cristianoag/msx-picoverse-public/docs/msx-picoverse-2040-features.md

# MSX PicoVerse 2040 Features

The MSX PicoVerse 2040 is a Raspberry Pi Pico-based MSX-compatible cartridge that offers a variety of features to enhance the MSX experience. Below is a list of its key features:

- **Multi-ROM Support**: The cartridge can store and run multiple MSX ROMs, allowing users to run different games and applications from a single cartridge.
- **Built-in Menu System**: A user-friendly menu system allows users to select and launch ROMs easily.
- **High Compatibility**: Supports a wide range of MSX ROMs, including games and applications for MSX1, MSX2, and MSX2+ systems.
- **Nextor DOS Support**: Compatible with Nextor DOS, enabling advanced file management and storage options.
- **Long Name Support**: Supports ROM names up to 50 characters, making it easier to identify games and applications.
- **Support for Various Mappers**: Includes support for multiple ROM mappers, enhancing compatibility with different types of MSX software. Mappers supported include: PL-16, PL-32, KonSCC, Linear, ASC-08, ASC-16, Konami, NEO-8, NEO-16, and others.
- **Support for up to 128 ROMs**: Can store and manage up to 128 different ROMs on a single cartridge.
- **Easy ROM Management**: Users can easily add, remove, and organize ROMs using a simple tool on their PC.
- **Fast Loading Times**: Utilizes the high-speed capabilities of the Raspberry Pi Pico to ensure quick loading times for games and applications.
- **Firmware Updates**: The cartridge firmware can be updated via USB, allowing users to benefit from new features and improvements over time.
- **Compact Design**: The cartridge is designed to fit seamlessly into MSX systems without adding bulk.
- **USB Mass Storage Support for Nextor**: Allows the use of the USB-C port as a mass storage device when running Nextor DOS.
- **RAM Mapper Support**: Enables the use of additional RAM for applications that require it when running Nextor DOS.
