cristianoag/msx-picoverse-public/2350/software/loadrom.pio/docs/log.md

# Change Log

## PicoVerse 2350 Loadrom v2.79

- Bumped LoadROM version to v2.79 (top-level `Makefile` and `tool/Makefile`).
- Added the `-s3` / `--sunrise3-sd` tool option for testing Nextor 3, microSD only for now. It builds a `Nextor Sunrise 3.0.0 Beta 2 (SD)` system image with Konamiman's Nextor 3.0.0 beta 2 Sunrise IDE MasterOnly kernel (`resources/Nextor-3.0.0-beta2.SunriseIDE.MasterOnly.ROM`, 128 KB, SunriseIDE-Nextor-driver `v0.1.8-blueMSX-v0.1.5-Nextor-3.0-beta.2` release), embedded by `tool/Makefile` as `tool/src/nextor3.h`. It uses the existing Sunrise SD type (15), so the firmware is unchanged; the beta 2 driver sends the same ATA commands as 2.1.4.
- `-s3` is mutually exclusive with the other Nextor modes, rejects a ROM file, `-d` and `-f` like `-s1`, and accepts `-w` (same loader as `-s1`). The tool refuses to build a Nextor image whose kernel is not 128 KB. Checked `-s3`, `-s3 -w` and `-s1` UF2s: the record points at the matching kernel bytes, and with `-w` the ESP8266P BIOS follows it. Booting beta 2 on hardware is not yet validated.
- Docs: LoadROM tool manual (`-s3`, `-w`, exclusivity, example, troubleshooting), Sunrise Nextor implementation notes (option table, MultiROM `-a`/`-s3`, and the stale `nextor/kernel/` paths now point at `resources/`), MegaRAM notes (same path fix), public README and WiFi notes.
- The shared generator `../tools/gen_romdb.py` now downloads the latest database by default from Vampier's ROM DB (`https://romdb.vampier.net/Archive/xml-msxromsdb.zip`) and reads `softwaredb.xml` from the zip in memory, so a local openMSX install is no longer needed. A local `softwaredb.xml` or `.zip` can still be passed as an argument for offline use. The generated header now records the source and the database timestamp. The script also accepts the `ASCII16-X` and lowercase `konami` mapper names used by this database.
- Regenerated `tool/src/romdb.h` from the 2026-10-03 database: 3115 → 3218 entries (103 added, none removed or changed), including 31 ASCII16-X ROMs (mapper 12) that the old DB never matched. Rebuilt `tool/dist/loadrom.exe`.

## PicoVerse 2350 Loadrom v2.78

- Simplified the standalone OPL4 (`-4`) generation options by removing `--opl4-limit` (adaptive PCM voice limiter) and `--lowclock` (282 MHz system clock). The tool now rejects both as unknown options, and `--22khz` is the remaining OPL4 option for extreme-polyphony songs.
- The OPL4 firmware always runs the RP2350 at 300 MHz (`OPL4_SYS_CLOCK_KHZ`) and always renders all 24 PCM voices: the voice-cap controller and its Core 1 hook were removed from `opl4_main.c`, and `ymf278b::generate` in `ymfm_opl.cpp` is back to the upstream `pcm_engine::ALL_CHANNELS` output mask. The per-buffer fill-time measurement is now only compiled in USB debug builds, and the debug report drops its `cap=` and `limit=` fields.
- The 16-byte `PVO4` config header between the firmware and the YRW801-M ROM is kept so the flash layout is unchanged; its flags byte is now reserved and always written as 0, and the firmware only uses the header to locate the ROM.
- Archived the removed code, grouped by the source file it came from, in `2350/software/old/loadrom_opl4_voice_limiter.c` and `2350/software/old/loadrom_opl4_lowclock.c`.
- Updated the LoadROM tool manual, the OPL4 implementation guide and the public readme to drop both options and point dense-song playback to `--22khz`.
- Bumped the loadrom build version to v2.78 (top-level and tool Makefiles), and regenerated the embedded 44.1 kHz and 22.05 kHz OPL4 firmware payloads.

## PicoVerse 2350 Loadrom v2.77

- Fixed the `.FLA` image being written to the microSD card empty, which left ASCII16-X FlashROM saves working only when a valid image happened to be there already. Creating the image was deferred until the MSX actually programmed the flash, and the file has to be opened with `FA_CREATE_ALWAYS`, which truncates it to zero straight away; the rest was then written only after the MSX had been quiet for a while. A game that saves and is then switched off left a zero-byte or partial file on the card, and because the restore path requires the file to match the emulated device size exactly, the next boot rejected it and started over. The image is now created in full during cartridge start-up, before the bus goes live, so the file on the card is always a complete, valid image.
- Bumped the loadrom build version to v2.77 (top-level and tool Makefiles).

## PicoVerse 2350 Loadrom v2.76

- Implemented the FlashROM half of the [ASCII16-X specification](https://www.grauw.nl/projects/ascii-x/ascii16-x/), so ASCII16-X cartridges can now erase and reprogram their own memory the way the real hardware does. Games and tools that use it for save games, high scores or user created levels work instead of silently failing.
- FlashROM emulation is opt-in through the `ASC16X-FR` filename tag, the same tag the Explorer tool uses, so a ROM tagged for one tool behaves the same way in the other. Auto-detection is unchanged: a ROM recognised as ASCII16-X is always built as the read-only variant, which keeps the previous behaviour and ignores flash command sequences entirely, so nothing changes for the ASCII16-X ROMs that never write to the cartridge. The two paths are separate bus loops, so the read-only one carries no extra work per bus cycle.
- Replaced the `-fr`/`--flashrom` option this feature originally shipped with; the tag is now the only way to select it, matching how every other mapper is forced in this tool. `ASC-16X-FR` is accepted as an alias, and `ASC16X` was added as an alias for the read-only variant so Explorer's spelling of both tags works here too.
- FlashROM stays a flag bit on mapper 12 rather than becoming a mapper number of its own as it is in Explorer (22). LoadROM packs the audio flags into the upper nibble of the mapper byte, so the firmware decodes a non-SYSTEM mapper as `rom_type & 0x0F` and only values 1-15 are addressable - mapper 22 would decode to 6 (ASCII16) and silently run the wrong mapper. The tag is what the user sees in both tools; only the on-flash encoding differs.
- The emulated device follows the AMD/Spansion command set the specification names as the guaranteed minimum: autoselect (`90h`), CFI query (`98h`), chip erase (`10h`), sector erase (`30h`), byte program (`A0h`) and the `F0h` software reset. Command addresses are decoded on A0-A11 (`XAAAh`/`X555h`), which is what the flash chip sees through the mapper, so a command cycle that lands on a bank register mirror updates both, exactly as on the cartridge.
- Sector geometry matches the layout the specification documents: eight 8KB boot sectors followed by 64KB sectors. Erasing clears the whole sector even when it spans several mapper banks.
- Erases run in 256-byte chunks between bus cycles instead of in one blocking pass, and while one is in progress every read returns a busy status byte (DQ7 low, DQ6 toggling, DQ3 set) rather than array data. That is the behaviour the specification tells software to poll for, and it keeps the MSX serviced throughout instead of stretching `/WAIT` for the length of the erase. Flash commands issued while an erase is running are ignored, as they are on the real device, so a stray program cannot corrupt the sector being erased and a second erase cannot abandon the first.
- The CFI records are built for the emulated device size at boot, so a driver that queries the chip gets a consistent description of the geometry it is being given. Only the commands that are actually implemented are advertised: no write buffer, no erase suspend and no sector protection, so CFI-driven software cannot pick a programming algorithm the cartridge does not support.
- Fixed flash chip detection failing outright (reported with "Go Figure v1.2", which reported no flash chip). The S29GL064S the ASCII-X cartridges use is a 16-bit device wired in byte mode, so the chip decodes command cycles on *word* addresses and places its identifiers and CFI records at word offsets, which the MSX sees at every second byte address. The emulation had been written as if the chip were an 8-bit part, so it looked for the unlock and query cycles at the wrong addresses and returned the identity bytes from the wrong offsets. Command decoding now ignores the lowest address bit, the CFI query is recognised at `X0AAh` instead of `X055h`, and the autoselect identifiers and CFI records are returned as 16-bit values split across even and odd byte addresses. Checked against the actual cycles the game issues: it queries CFI with `98h` to `40AAh` and reads `4020h`/`4022h`/`4024h` for `QRY`, then unlocks with `AAh` to `4AAAh` and `55h` to `4554h` before `90h` selects autoselect and it reads the manufacturer at `4000h` and the device identifiers at `4002h`, `401Ch` and `401Eh`. Note that the sector erase and byte program sequences were unaffected, because the address the game uses for their second unlock cycle happened to satisfy the old check as well.
- Reworked where the flash array lives. With the tag applied, the cartridge ROM is staged into the external PSRAM at boot and that copy is the writable flash array, with the existing 256KB SRAM bank cache in front of it so MSX reads are still served from internal SRAM at full speed. The previous flash handling only modified the SRAM cache, so any write was lost as soon as its bank was evicted, and a bank refill re-read the unmodified ROM from flash.
- With the tag applied, the emulated device is sized to the next power of two at or above the ROM size (minimum 64KB, capped at the 8MB PSRAM), so banks past the end of the ROM read as erased (`FFh`) and out-of-range bank numbers wrap at the device size, matching a real cartridge. The read-only path keeps wrapping at the ROM size as before.
- Added `storage/flash_sd.c`, which mirrors the flash array to a `.FLA` file in the root of the microSD card named after the cartridge, so flash writes survive a power cycle. The file has no header: it is a byte exact image of the cartridge flash and can be copied off the card and used as a ROM image.
- At boot Core 1 mounts the card and restores the image when a file of the expected size is present. The MSX is held in `/WAIT` for that read, and the bus is only released once Core 1 has finished with the array so the bank cache can never be filled from a half-restored image. When no usable image is present nothing is written at boot: creating one means writing the whole array to the card, which takes seconds on a multi-megabyte cartridge, so it is deferred until the MSX actually programs the flash and then runs on Core 1 with the bus already live. A card that has never been saved to therefore costs nothing at startup. Afterwards Core 1 writes back only the 4KB blocks the MSX modified, and only once the MSX has left the flash alone for 250 ms, so a burst of byte programs turns into a handful of card writes. A failed restore falls back to the embedded ROM rather than leaving a half-replaced image behind, and a block whose write or sync fails is put back on the queue instead of being dropped.
- Flash emulation degrades gracefully: without working PSRAM the mapper still runs from the ROM in firmware flash, and without a usable microSD the flash is emulated normally but is volatile. Persistence is also skipped when `-d` (second PSG) is used with an ASCII16-X ROM, because that emulation already owns the core that writes the card.
- The PC tool now reports whether FlashROM emulation is on for ASCII16-X ROMs, and when it is, the emulated device size and the name of the `.FLA` image it will use. It warns when `-d` disables persistence, lists `ASC16X-FR` among the forceable tags in `-h`, and tells the user which tag to apply when a ROM was detected as plain ASCII16-X.
- Bumped the loadrom build version to v2.76 (top-level and tool Makefiles).

## PicoVerse 2350 Loadrom v2.75

- Fixed OPL4/MoonSound images (`-4`, with or without `--22khz`) playing much quieter than the SCC, PSG and MSX-MUSIC audio profiles, which forced the amplifier or TV volume to be turned far up for an OPL4 game and back down again afterwards (reported with "Go Figure"). The YMF278B emulation core applies no output normalisation to this chip - upstream marks its YMF278B mixing as unverified - so the cartridge was running about 7 dB below the level the same hardware plays SCC/PSG music at. The final output stage now applies a 3x gain, which lines the OPL4 up with the other profiles.
- The gain was calibrated against openMSX, whose wave part is matched to real MoonSound recordings, by comparing the peak one voice or channel can contribute to an output channel: openMSX puts a MoonSound wave voice at 0.292 of full scale, an SCC channel at 0.102 and a PSG channel at 0.255, while the PicoVerse firmware puts its SCC channel at 0.200 and its PSG channel at 0.498 - a consistent ~1.96x above openMSX - against only 0.85x for the OPL4 wave voice. The FM/wave balance is unchanged: both halves of the emulated chip already peak at the same per-channel level openMSX gives them, so the correction is a single gain on the mixed output and the chip's own mix registers (0xF8/0xF9) still set the balance.
- Replaced the hard clip on the OPL4 output with the same soft-knee limiter the SCC and MSX-MUSIC profiles use. The chip can key 24 wave voices and 18 FM channels at once, so a sum over full scale is normal on dense songs; the mix is now compressed smoothly toward full scale instead of being squared off into harsh buzz, and a single maximum-level voice still passes through untouched.
- Added `OPL4_OUTPUT_GAIN_NUM`/`OPL4_OUTPUT_GAIN_SHIFT` CMake options (default 96/32 = 3x) so the output level can be A/B tested from the build configuration alone.
- The OPL4 USB debug report now prints `lim/s` (samples pushed past the limiter knee) in place of `clip/s`, which measured a hard clip that no longer exists.
- Bumped the loadrom build version to v2.75 (top-level and tool Makefiles), and regenerated the embedded 44.1 kHz and 22.05 kHz OPL4 firmware payloads.

## PicoVerse 2350 Loadrom v2.74

- Added the `--22khz` option to the standalone OPL4 mode (`-4`). It builds an OPL4 cartridge image that renders audio at 22050 Hz instead of 44100 Hz, roughly halving the emulation workload. This is meant for the handful of very dense songs (reported with "Go Figure") that use so many simultaneous FM channels and wave voices that the 44.1 kHz emulation cannot keep up in real time and breaks into continuous noise. The trade-off is a duller high end and more aliasing on bright FM patches, cymbals and high-pitched samples, so the option is opt-in and the default 44.1 kHz image remains the recommended one.
- The 22 kHz image still emulates every FM channel and wave voice at full polyphony: instead of dropping voices, each generated sample simply covers twice as much chip time, with the wave positions, FM phase, envelopes and LFOs advanced accordingly so pitch, tempo and envelope timing are unchanged.
- The OPL4 USB debug report now includes the output sample rate, so a capture states which of the two images produced it.
- Fixed occasional video glitches seen when a game running from a second cartridge shares the MSX with a `--22khz` OPL4 cartridge. The wave part reports a "loading" status bit for about 300 us after every instrument change, and music drivers poll that bit before continuing. The delay was counted in generated samples rather than in real time, so at 22050 Hz it lasted twice as long, doubling the time the MSX spent in that polling loop - long enough to push a raster-timed game routine past its deadline. The count is now scaled with the output rate, so the host sees the same 300 us in both images.
- Fixed notes sounding too quiet, or not being heard at all, on some songs with `--22khz`. The fastest wave envelope rates step on every emulated sample period, so at the reduced output rate they were advancing at half speed. Short percussive notes never reached full volume before the next event, and the fast "damp" used to silence a voice before reassigning it took twice as long. Both the wave and FM envelope generators now replay the sample periods a reduced-rate build steps over, and were verified against the 44100 Hz build to better than half a percent across the whole attack and release.
- Fixed missing FM notes, most noticeable on songs using many FM channels (reported with "Neon Horizon"). A note retrigger writes key-off then key-on for the same channel, and the FM part only looked at the key signal once per generated sample, so a retrigger that arrived inside one sample collapsed into "still on" and the note never restarted. This is the same defect that was fixed for the wave part in v2.72, and it applied to the FM part as well; it shows up far more often with `--22khz` because that sample window is twice as long and the cartridge applies a whole burst of MSX writes between two samples. Key changes are now applied in the order the MSX issues them. Debug captures ruled out the alternatives: the emulation was comfortably real-time throughout, with no late buffers, no dropped writes and no clipping.
- Fixed OPL4 debug builds not being detected by software that probes for the cartridge at boot. The debug firmware waits up to five seconds for a USB host to attach, and that wait ran before the cartridge brought up its MSX bus responder, so the OPL4 was absent from the bus for the whole timeout and a game checking for it at startup (reported with "Neon Horizon") ran without music. The wait now happens after the bus is live. Production builds were never affected.
- Bumped the loadrom build version to v2.74 (top-level and tool Makefiles).

## PicoVerse 2350 Loadrom v2.73

- Fixed hanging notes in OPL4 playback, most noticeable at music transitions (reported with Bombaman). The wave part has a "pseudo-reverb" feature that lets a note ring out at a fixed slow rate once it drops below -18 dB. That state was also being entered *after* the MSX had already released the note, and it overrode both the instrument's own release rate and the damp command the music driver uses to silence a voice, so released notes kept sounding for many seconds instead of stopping. Pseudo-reverb is now only entered while a note is still held, and an explicit key-off always takes a released voice back to its programmed release rate. Debug telemetry confirmed the cause: during every hang the firmware reported that all the ringing voices had already been released by the MSX.
- Fixed occasional dropped OPL4 register writes during normal playback. The audio core holds the emulation lock for the whole of each generated sample - about two thirds of the time available - so the bus core could sit blocked long enough for the 8-entry hardware write FIFO to fill and silently lose MSX writes. The bus core now keeps emptying that FIFO into its much larger software queue while it waits for the lock, and also between register writes, which can each take a while when a new instrument has to be fetched from memory. Debug captures had shown the overflow flag being raised in 8 of 118 seconds of Bombaman playback.
- Added the voices sitting in the pseudo-reverb envelope (`pcmRev`) to the OPL4 USB debug report, so a hanging-note report can be checked against the envelope state that causes it.
- Bumped the loadrom build version to v2.73 (top-level and tool Makefiles).

## PicoVerse 2350 Loadrom v2.72

- Fixed missing instruments in OPL4 MOD playback (reported with MOP playing `enigma.mod`). A note retrigger writes key-off then key-on for the same voice, and when both arrived within the same emulated sample the pair was merged into a single "still on" state, so the note never restarted and that voice fell silent. Key changes are now applied in the order the MSX issues them.
- Fixed audible clicks, crackle and noise on dense OPL4 songs (reported with Bombaman and Pumpkin Adventure 3). The emulation was spending most of its per-sample time budget on voices that were silent, leaving it right at - and sometimes over - the real-time limit, which starved the audio output. Silent voices are now skipped, cutting the load to roughly a quarter of the budget.
- Fixed hanging and delayed notes caused by the cartridge freezing the MSX for about 150 us on every OPL4 register read. During read bursts this stole up to a quarter of the CPU time from the running music replayer. The read handler now answers about fifteen times faster, which also makes OPL4 sample uploads roughly three times quicker.
- Fixed the optional adaptive voice limiter (`--opl4-limit`) leaving hanging notes: dropped voices froze mid-note instead of being silenced, and resumed where they left off when the limiter recovered.
- Improved the OPL4 USB debug report with true output-clipping detection, the number of voices actually being rendered, and the voices the MSX asked to play, so audio complaints can be traced to the right stage. Removed some per-sample debug work that was distorting the timing figures it reported.
- Extended the OPL4 USB debug report with the key-offs the MSX issued and the voices still sounding after being released (`pcmOff`, `pcmRel`), which separates a lost key-off from a release envelope that simply takes a long time to fade - both are heard as a hanging note.
- Added build options to individually disable this version's OPL4 changes (`OPL4_SKIP_INACTIVE_FM`, `OPL4_SKIP_INACTIVE_PCM`, `OPL4_READ_SYNC_IDLE_SPINS`) so a regression can be narrowed down from the build configuration alone. Defaults keep all the fixes enabled.
- Bumped the loadrom build version to v2.72 (top-level and tool Makefiles).

## PicoVerse 2350 Loadrom v2.71

- Bumped the loadrom build version to v2.71 (top-level and tool Makefiles).
- Fixed the standalone OPL4 firmware asserting `/BUSDIR` on bus cycles that do not belong to it. The dedicated `/BUSDIR` state machine inferred "an OPL4 read is in progress" purely from `/WAIT` being low, but `/WAIT` is a shared open-drain MSX bus signal, so any second cartridge stretching its own cycles made the OPL4 flip the main-board data-bus buffer towards the CPU. `msx_opl4_busdir` now tests `/IORQ` (new `jmp_pin`, matching the MSX-AUDIO firmware) before asserting, so memory cycles driven by another cartridge are ignored.
- Changed the standalone OPL4 write captor (`msx_opl4_io_write`) to commit register/memory writes on the `/WR` rising edge. The GPIO snapshot is still taken well inside `/WR` low, where the Z80 write data is valid, but the RX FIFO push (which triggers the PIO IRQ and the `opl4_bus_write()` call) was happening before `wait 1 gpio 25`, so the emulated YMF278B could apply a write while the CPU had not finished the bus cycle. The push now happens after the `/WR` rise, matching how a real chip latches.
- Applied the same `/WR` rising-edge commit to the standalone MSX-AUDIO firmware: both `msxaudio_io_write` (Y8950 ports 0xC0/0xC1) and `msxaudio_mem_write` (ADPCM sample RAM window) now sample the bus inside `/WR` low but only push to the RX FIFO once `/WR` has risen.

## PicoVerse 2350 Loadrom v2.70

- Bumped the loadrom build version to v2.70 (top-level and tool Makefiles).
- Fixed lost bank-switch writes in the ASCII16, ASCII16-X, Neo-8 and Neo-16 mapper loops. Those loops blocked in `pio_get_read_servicing_dual_psg()` and only drained the memory write captor FIFO *after* a cartridge read arrived, so game code executing from MSX RAM that issued a burst of segment switches without any intervening cartridge read overflowed the 8-entry RX FIFO. The write state machine then stalled on `push block` and the extra switches were silently dropped, leaving the mapper register on a stale segment (and, with an ASCII16-X cache miss, forcing the 16KB bank refill to run while `/WAIT` was already asserted). Added `pio_get_read_draining_writes()`, which services the dual-PSG I/O and drains the memory write FIFO while waiting for the next read, and switched the four loops to it. Reported with "Go Figure v1.2" (ASCII16-X), which alternates the page-1 segment twice per call from a page-3 RAM routine and hung on the palette cross-fade. The Konami/Konami-SCC/ASCII8 `banked8_loop` already drained writes while idle and was unaffected.
- Kept the idle loop at the same read-response latency as a plain blocking wait by sampling `FSTAT` once per iteration and testing the read and write RX-empty flags from that single sample. Polling the two FIFOs with separate `pio_sm_is_rx_fifo_empty()` calls doubles the PIO register accesses in the loop, which stretches `/WAIT` on every cartridge read enough to slow VDP transfer loops and trigger "VDP too slow" reports in timing-sensitive games (observed on the RP2040 build). `banked8_loop` now shares the same helper instead of its own inline poll, so Konami/Konami-SCC/ASCII8 reads got the same latency reduction.

## PicoVerse 2350 Loadrom v2.69

- Bumped the loadrom build version to v2.69 (top-level and tool Makefiles) and added the `msxaudio` build target, with `tool` depending on it.
- Reorganized `pico/loadrom` sources into per-type subfolders: `audio/` (`emu2149`, `emu2212`, `emu2413`), `memory/` (`c2_emu`, the Carnivore2-style mapper/RAM emulation), and `storage/` (`hw_config`, `sunrise_ide`, `sunrise_sd`), updating `CMakeLists.txt` and `loadrom.c` includes accordingly. Verified with a full reconfigure and rebuild.
- Removed the unused `wifi_uart.pio` PIO program (superseded by the hardware UART1 ESP-01 backend) and updated the `CMakeLists.txt` comment accordingly.
- Moved `nextor/kernel/Nextor-2.1.4.SunriseIDE.MasterOnly.ROM` into `resources/`, updated the `NEXTOR_SUNRISE` path in `tool/Makefile`, and fixed the resulting `xxd`-generated embed symbol names in `tool/src/loadrom.c`.
- Added a new standalone MSX-AUDIO (Yamaha Y8950) cartridge firmware, selectable with the new `-a` / `--msx-audio` tool option. The cartridge emulates a Y8950 on I/O ports 0xC0/0xC1 with 256KB of ADPCM sample RAM and exposes the MSX-Audio BIOS in its own slot, so MSX-AUDIO software runs on real hardware without an original card. The option is standalone and cannot be combined with any other mode or a ROM file. Issue #25.
- Used the BSD-licensed ymfm `y8950` core for the emulation, kept as a private copy under the new firmware so it does not share sources with the standalone OPL4 firmware. Fixed an upstream ymfm defect that made ADPCM sample RAM read-backs always return 0.
- Added Y8950 FM timer interrupts through the MSX `/INT` line so timer-paced MSX-AUDIO replayers run at the correct tempo, and drove `/BUSDIR` during MSX-AUDIO port reads to avoid bus contention when a second cartridge is installed.
- Added the MSX-AUDIO-only `--4mhz` option, which clocks the emulated Y8950 at 4 MHz instead of the standard 3.579545 MHz. Partially related to issue #33.
- Fixed MSX-AUDIO instruments sounding harsher and different from openMSX on some games (reported with "Wolf of the Battlefield - Commando"). The emulated Y8950 output already leaves the sound core as a full-scale, DAC-clipped 16-bit sample, so the extra 1.5x volume boost that the other PicoVerse audio profiles use was clipping it a second time on loud passages and adding distortion harmonics. The MSX-AUDIO output now runs at unity gain.
- Added `docs/msx-picoverse-2350-msx-audio.md` with the full MSX-AUDIO implementation documentation.
- Documented the standalone MSX-AUDIO (`-a`, `--4mhz`) and OPL4 / MoonSound (`-4`, `--opl4-limit`, `--lowclock`) builds in `docs/msx-picoverse-2350-features.md`, `docs/msx-picoverse-2350-loadrom-tool-manual.en-us.md`, and `docs/msx-picoverse-public-readme.md`, including slot/port maps, sample RAM, `/INT` timer behavior, output rates, standalone mutual-exclusion rules, troubleshooting rows, and MSX-AUDIO credits. Also corrected the manual's stale OPL4 `--22khz` option, which no longer exists in the tool.
- Known limitations: the Philips NMS-1205 MIDI interface and the Music Module's 8-bit DAC on port 0x0A are not emulated.

## PicoVerse 2350 Loadrom v2.68

- Removed the OPL4-only `--22khz` build option and its alternate 22050 Hz standalone firmware payload after validation showed missing instruments and notes in OPL4 playback. The tool now always packages the default 44100 Hz standalone OPL4 firmware for `-4` / `--opl4` images.
- Simplified the standalone OPL4 build and embedding pipeline back to a single firmware artifact (`opl4.bin`) so the main build no longer configures, compiles, embeds, or cleans a separate 22.05 kHz variant.
- Version bumped to v2.68 (top-level and tool Makefiles).

## PicoVerse 2350 Loadrom v2.67

- Added the OPL4-only `--22khz` tool option for `-4`/`--opl4` images. The build now produces and embeds a second dedicated OPL4 firmware payload compiled for 22050 Hz; that variant advances FM/PCM/timer state by two normal OPL4 sample periods per generated output sample so pitch and tempo stay at normal speed while reducing output-rate workload. Default OPL4 UF2s continue to use the 44100 Hz firmware.
- Version bumped to v2.67 (top-level and tool Makefiles).

## PicoVerse 2350 Loadrom v2.66

- Fixed the PC tool mapper-detection read path to reject truncated ROM reads before hashing or scanning the allocated ROM buffer.
- Version bumped to v2.66 (top-level and tool Makefiles).

## PicoVerse 2350 Loadrom v2.65

- Bumped the loadrom build version to v2.65.
- Gated the standalone OPL4 USB diagnostic counters out of production builds so timer/IRQ debug increments and output peak globals are only compiled when `OPL4_USB_DEBUG` is enabled.

## PicoVerse 2350 Loadrom v2.64

- Bumped the loadrom build version to v2.64.
- Added `-r1`/`--megaram-sd` and `-r2`/`--megaram-usb` Nextor system images with the existing Sunrise IDE ROM, a 1MB MSX memory mapper, and a new 1MB PSRAM-backed MegaRAM subslot.

## PicoVerse 2350 Loadrom v2.63

- Tuned the standalone OPL4 adaptive PCM voice limiter to be less aggressive: it now lowers the voice cap only after sustained late buffers, restores voices after repeated headroom, and keeps a higher minimum cap so melodic leads are less likely to be ducked when `--opl4-limit` is enabled.

## PicoVerse 2350 Loadrom v2.62

- Bumped the loadrom build version to v2.62.
- Expanded the standalone OPL4 `OPL4DBG` USB CDC report with timer, read latency, write FIFO/ring-drop, limiter, and clock-mode counters for field captures of missing-instrument issues, while keeping USB CDC disabled by default for normal timing validation. Left enabled by default so we can capture data in case of future reports of missing instruments or other audio issues.
- Added the OPL4-only `--lowclock` tool option for `-4`/`--opl4` images; default OPL4 UF2s keep the 300 MHz RP2350 clock, while `--lowclock` marks the OPL4 config header so the firmware boots at 282 MHz. This is to cover low quality PSRAM modules that cannot sustain the 300 MHz clock at full polyphony, which can cause audio underruns and missing instruments. The firmware reads the config header and sets the RP2350 clock divider to 282 MHz if the option is present.
- Raised the standalone OPL4 firmware's final I2S output gain to better match the SCC, MSX-MUSIC, and other emulated audio profiles while preserving signed 16-bit clipping protection (issue reported by Peter).
- Regenerated the embedded standalone OPL4 firmware payload and rebuilt the loadrom tool so the `loadrom -4` image uses the intended 300 MHz RP2350 clock instead of a stale 250 MHz binary (issue reported by Peter).

## PicoVerse 2350 Loadrom v2.61

- Updated the public README OPL4 credits to describe the PicoVerse 2350 standalone MoonSound firmware architecture, host-port handling, YMF278B/ymfm wrapper, YRW801-M ROM/RAM model, and third-party reference/ROM attribution more accurately.
- Fixed Neo-8/Neo-16 ROMs not launching when MSX-MUSIC/FM-PAC (`-f` / `-fmpac`) is enabled (the same ROM booted fine without `-f`). The FM-PAC expanded-slot launcher reset the Neo-8/Neo-16 bank windows to `{0,1,2,...}`, exposing segment 1 at MSX `0x4000`, so the cartridge "AB" boot header (which lives in segment 0) was hidden during the BIOS expanded-slot scan and the MSX dropped to BASIC. The windows now power on at segment 0 (`{0,0,0,...}`), matching the standalone `loadrom_neo8`/`loadrom_neo16` loaders, so the header is visible at `0x4000` and the game launches alongside FM-PAC.
- Fixed MSX-MUSIC/FM-PAC ROMs (`-f` / `-fmpac`) booting to BASIC instead of launching the game. The firmware was starting the YM2413 Core 1 + I2S audio output in `main()` *before* `loadrom_fmpac()` ran the expanded-slot cold-boot bootstrap, so the running audio core/DMA perturbed the timing-critical FM-PAC bus handshake and the MSX dropped to BIOS. The audio output launch (`msx_music_start_audio()`) is now deferred until after the bootstrap completes and `msx_pio_bus_init()` has brought the FM-PAC bus responder live — matching the Explorer ordering ("start MSX-MUSIC audio output only after the FM-PAC ROM bus initialization releases `/WAIT`"). `main()` now only runs `msx_music_init()` (emulator setup) for the MSX-MUSIC audio mode.
- Refreshed the generated ROM mapper SHA1 database from the current openMSX `softwaredb.xml` and updated the shared generator to parse the new attribute-based XML format.
- Changed the standalone OPL4 cartridge `/BUSDIR` driver from open-drain to push-pull so it matches a real OPL4/MoonSound cartridge (the WozBlaster CPLD drives `/BUSDIR = /RD & /CS` as a continuous push-pull output). The dedicated PIO2 state machine now drives the line actively HIGH when released and LOW only while answering an OPL4 I/O read, instead of releasing it to hi-Z. The previous open-drain release could let the MSX data-bus-buffer direction input float during register writes on machines without a strong `/BUSDIR` pull-up, occasionally corrupting OPL4 register writes and dropping instruments from some songs; driving it push-pull keeps the buffer direction defined at all times.
- Added an optional adaptive PCM voice limiter to the standalone OPL4 cartridge, selectable at programming time with the new `loadrom -4 --opl4-limit` option. Extreme-polyphony homebrew (e.g. Neon Horizon) drives the full YMF278B ~1.6-1.9x past the single-core real-time synthesis budget, underrunning the I2S and producing harsh broken audio. When the limiter is enabled, Core 1 measures its own per-buffer fill time and dynamically lowers the number of rendered PCM voices (`ymf278b::generate` renders only voices `[0, cap)`) just enough to stay real-time, raising the cap back toward the full 24 when the load eases. Light passages stay bit-identical; only the densest peaks shed their highest-numbered PCM voices, trading some peak polyphony for continuous, in-tune playback instead of underrun noise. The option is off by default (full fidelity, may underrun on extreme songs); the firmware reads the choice from a 16-byte config header the tool writes between the firmware image and the appended YRW801-M ROM.

## PicoVerse 2350 Loadrom v2.60

- Bumped the loadrom version to v2.60.
- Major OPL4/MoonSound overhaul with a new dual-core architecture on the RP2350, significantly improving compatibility, stability, and performance.
- Full MoonSound support now working correctly, including successful operation with MoonTest, SETOPL4, MBWAVE, and MoonBlaster.
- Fixed critical OPL4 emulation issues, improving compatibility with software that relies on accurate YMF278B behavior, status reporting, and memory access.
- Added proper OPL4 timer interrupt support through the MSX /INT line, allowing music players and replayers to run at the correct tempo.
- Corrected FM timer timing, fixing playback speed problems that previously caused some MoonSound applications to run extremely slowly.
- Improved audio synthesis performance, enabling real-time playback at full polyphony through SRAM execution, optimized memory access, and a 300 MHz RP2350 clock speed.
- Redesigned the OPL4 write handling path, eliminating dropped register writes during heavy audio workloads and improving reliability in complex games and music software.
- Updated /WAIT signal handling to use open-drain behavior, preventing conflicts when multiple cartridges are installed in the MSX.
- Held /WAIT asserted during the brief OPL4 boot initialization so the Z80 (and any game in another cartridge slot) is frozen until the cartridge's bus responder is live, fixing cases where a second cartridge's game started — and began its MoonSound music — before the OPL4 cartridge was ready. The hold spans only the sub-millisecond PSRAM/ymfm bring-up (well under the Z80 DRAM-refresh limit) and is released when the PIO takes over /WAIT; the PSRAM-init failure path releases /WAIT so the MSX can still boot.
- Added advanced OPL3 diagnostic capabilities to investigate remaining audio differences in a small number of FM-only titles.
- Compiled the YMF278B synthesis core (the ymfm sources and the `emu278b` wrapper) at `-O3 -funroll-loops` instead of the SDK default `-O2`, since they are the firmware's hottest per-sample path and sit at the real-time budget under maximum polyphony. The change is optimization-only (bit-identical audio) and gives extra instruction-level throughput; it does not fully resolve the documented extreme-polyphony ceiling but recovers a small amount of headroom.
- Drove the MSX `/BUSDIR` line (GPIO 37) during OPL4 I/O read responses, matching how a real OPL4/MoonSound cartridge behaves (the WozBlaster CPLD asserts `/BUSDIR = /RD & /CS`). The cartridge now flips the MSX main-board data-bus buffer toward the CPU only while it answers one of its own ports (0x7E/0x7F, 0xC4-0xC7) and drives D0-D7; otherwise `/BUSDIR` is released hi-Z (open-drain). Previously `/BUSDIR` was left as an unused input, so the firmware's data-bus drive fought the host's slot data buffer on every OPL4 read — visible as screen flashing / graphics artifacts (without a freeze) when a game in another cartridge slot was also driving the bus. Because `/BUSDIR` (GPIO 37) lies outside the 32-pin window the read/write state machines use for A0-A7, it is driven by a dedicated state machine on PIO2 (GPIO base 16) that mirrors the read responder's selection: it holds `/BUSDIR` low from the moment the read SM asserts `/WAIT` for an OPL4 port until `/RD` is released.
- Removed the temporary `OPL4_DRIVE_INT` diagnostic build switch; the `/INT` line is once again always driven from the YMF278B FM-timer interrupt. The switch had been added to test whether the maskable-interrupt path caused the multi-cartridge graphics-corruption crash, but that was ruled out — the cause was the missing `/BUSDIR` drive above.
Production-ready release, with hardware validation completed and accompanying implementation documentation added.

## PicoVerse 2350 Loadrom v2.59

- Bumped the loadrom sub-project version to v2.59.
- Added a dedicated, standalone OPL4 / YMF278B / MoonSound / WozBlaster cartridge firmware under `pico/opl4/`. This firmware implements a MoonSound-compatible OPL4 register interface and exposes the YRW801-M ROM as directly mapped wave memory, allowing it to pass the full MoonTest OPL4 detection and RAM test sequence without any host-side patches or timing compromises. The cartridge is built with the new `-4` / `--opl4` option in the loadrom tool, which produces a firmware-only UF2 with the OPL4 firmware and YRW801-M ROM embedded back-to-back in flash; this option is mutually exclusive with all other modes and external ROM files.
- Tightened the standalone OPL4 read/write synchronization window so `/WAIT`-held reads only proceed after the decoded write FIFO is empty and `/WR` has remained released long enough for rare MoonTest RAM readback edges.
- Added lock-free FM and wave register readback shadows for software such as MBWAVE that probes the cartridge by reading back recently written OPL4 register/data ports.
- Expanded the standalone OPL4 lock-free host facade to mirror the YMF278 PCM register file more completely: reset defaults, masked device/control bits, address-register auto-increment readback, memory-data readback, and queued PCM control/register writes for the audio core while keeping host memory transfers direct and non-busy.
- Reduced sporadic MoonTest RAM-test errors by keeping PCM memory-window control/address writes local to the lock-free host facade while memory access mode is active, using volatile PSRAM byte accesses for host RAM transfers, and sampling decoded MSX write data later inside the `/WR` low window.
- Removed the experimental Core1 synthesis pause because it did not improve MoonTest RAM stability and could interfere with repeated SETOPL4 `/P` ROM sample playback when tools leave the memory-access-mode bit enabled.
- Hardened USB diagnostics so debug builds never enqueue per-byte `0x7F`/wave-register-`0x06` memory read/write events while memory access mode is active, preventing MoonTest RAM loops from flooding the debug ring and perturbing bus timing.
- Changed the standalone OPL4 audio core to drain queued ymfm writes before each small audio chunk instead of once per 256-sample audio buffer, reducing key-on, wavetable, mixer, SETOPL4, and MBWAVE register latency without the per-sample locking overhead that made tracker playback crawl.

## PicoVerse 2350 Loadrom v2.58

- Bumped the loadrom sub-project version to v2.58.
- Raised the MSX-MUSIC/FM-PAC audio output gain to match the existing SCC, SCC+, and Dual PSG I2S volume boost while preserving sample clipping protection.
- Fixed embedded Sunrise+Mapper SD and Carnivore2 SD/USB type decoding so system type values 16-18 are not mistaken for audio-flagged external ROMs.

## PicoVerse 2350 Loadrom v2.57

- Bumped the loadrom sub-project version to v2.57.
- Added dual PSG emulation: a secondary AY-3-8910 instance (emu2149) clocked at 1.7897725 MHz that captures `OUT (0x10),A` / `OUT (0x11),A` on the MSX I/O bus via a dedicated PIO1 write captor and streams its mix to the I2S DAC alongside the existing SCC audio path.
- Added the loadrom tool `-d` / `--dual-psg` flag that sets bit 4 of the configuration `rom_type` byte; the firmware reads this flag at boot to enable the dual PSG engine.
- Centralised cartridge audio configuration in the firmware as a single mutually-exclusive `audio_mode_t` (`NONE` / `SCC` / `SCC_PLUS` / `DUAL_PSG`) so future on-cartridge sound chips can be plugged in without conflicting with existing engines.
- Enforced audio-mode exclusivity in the tool: `-d` is rejected against `-scc`/`-sccplus`, against Konami SCC and Manbow2 mappers (whose second audio slot is reserved for the on-cartridge SCC chip), and against the embedded Sunrise/Carnivore2 system modes that already use core 1 for storage backends.
- Simplified the `-d` rejection message for Konami SCC / Manbow2 ROMs to "Second PSG is not supported with Konami SCC ROMs."
- Moved dual PSG I/O servicing to core 1 (the audio producer core) so secondary PSG port writes are consumed continuously even while game code runs from MSX RAM and no cartridge read cycles occur.
- Delayed the PIO1 I/O write sample point inside `/WR` low so plain `0x10`/`0x11` port writes are latched after the address and data lines have fully settled.
- Added the shared PicoVerse 2350 Dual PSG implementation reference covering LoadROM and Explorer behavior.
- Added MSX-MUSIC/YM2413 emulation for non-SYSTEM ROMs through `-f` / `-fmpac`, capturing OPLL writes on I/O ports `0x7C`/`0x7D` via PIO1 and streaming emu2413 audio through the I2S DAC.
- Enforced MSX-MUSIC as a mutually-exclusive cartridge audio mode with SCC, SCC+, and Dual PSG; documented the emu2413 credit in the public README.
- Embedded the English FM-PAC BIOS (`FMPCCMFC.BIN`) into the LoadROM tool output for every `-f` / `-fmpac` non-SYSTEM ROM image and exposed it from the firmware through an expanded FM-PAC subslot.
- Added firmware handling for FM-PAC memory-mapped YM2413 registers (`0x7FF4`/`0x7FF5`), FM-PAC control/page registers, and PAC SRAM key gating while preserving the selected game mapper in the primary subslot.
- Updated the 2350 LoadROM manual and public copyright notes to describe FM-PAC BIOS inclusion and credit the bundled BIOS/translation sources.
- Added a detailed PicoVerse 2350 MSX-MUSIC / FM-PAC implementation guide covering the tool packaging, UF2 layout, firmware audio path, expanded-slot BIOS exposure, mapper routing, and limitations.
- Updated the public README with user-facing LoadROM instructions for MSX-MUSIC/FM-PAC and Dual PSG command-line builds.
- Removed Konami SCC and Manbow2 from the supported MSX-MUSIC/FM-PAC mapper set; the LoadROM tool now rejects `-f` / `-fmpac` for those ROMs and the firmware FM-PAC wrapper no longer carries SCC-class mapper branches.
