cristianoag/msx-picoverse-public/2350/software/explorer.pio/msx/src/menu_ui.c

// MSX PICOVERSE PROJECT
// (c) 2026 Cristiano Goncalves
// The Retro Hacker
//
// menu_ui.c - MSX Explorer menu screen rendering and text-mode handling
//
// This work is licensed  under a "Creative Commons Attribution-NonCommercial-ShareAlike 4.0 International
// License". https://creativecommons.org/licenses/by-nc-sa/4.0/

#include <string.h>
#include <stdint.h>
#include "menu_ui.h"
#include "menu.h"
#include "menu_input.h"

__at (BIOS_HWVER) unsigned char msx_version;
__at (BIOS_LINL40) unsigned char text_columns;
__at (BIOS_RG4SAV) unsigned char vdp_reg4;

#define MENU_UI_HLINE_SOURCE_CHAR 0x17
#define MENU_UI_HLINE_PRINT_CHAR  0x7E

static unsigned char menu_ui_render_shortcuts(unsigned char content_width);
static unsigned char menu_ui_shortcuts_length(void);

static void clear_rows_vram(unsigned char start_row, unsigned char end_row, unsigned char width) __naked
{
    (void)start_row;
    (void)end_row;
    (void)width;
    __asm
    ld      hl, #2
    add     hl, sp
    ld      e, (hl)
    inc     hl
    ld      d, (hl)
    inc     hl
    ld      c, (hl)

    ld      a, d
    sub     e
    jr      z, clear_rows_done
    ld      b, a

    ld      hl, (#BIOS_TXTNAM)
    ld      a, e
    ld      e, c
    ld      d, #0
    or      a
    jr      z, clear_rows_calc_done

clear_rows_calc_loop:
    add     hl, de
    dec     a
    jr      nz, clear_rows_calc_loop

clear_rows_calc_done:
clear_rows_loop:
    push    bc
    push    de
    push    hl
    ld      a, #32
    ld      b, #0
    ld      iy,(#BIOS_EXPTBL-1)
    push    ix
    ld      ix,#BIOS_FILVRM
    call    BIOS_CALSLT
    pop     ix
    pop     hl
    pop     de
    pop     bc
    add     hl, de
    djnz    clear_rows_loop

clear_rows_done:
    ret
    __endasm;
}

// blit_row_vram - Copy `width` bytes from a RAM buffer straight into the text
// name table at the given row using BIOS LDIRVM, replacing per-character CHPUT. 
static void blit_row_vram(unsigned char row, const char *src, unsigned char width) __naked
{
    (void)row;
    (void)src;
    (void)width;
    __asm
    ld      hl, #2
    add     hl, sp
    ld      b, (hl)        ; B = row
    inc     hl
    ld      e, (hl)        ; src low
    inc     hl
    ld      d, (hl)        ; DE = src
    inc     hl
    ld      c, (hl)        ; C = width

    push    de             ; save src
    push    bc             ; save row(B) + width(C)

    ; dest = TXTNAM + row * width
    ld      l, c           ; HL = width
    ld      h, #0
    ex      de, hl         ; DE = width
    ld      hl, #0
    ld      a, b           ; A = row
    or      a
    jr      z, blit_addr_done

blit_addr_loop:
    add     hl, de
    dec     a
    jr      nz, blit_addr_loop

blit_addr_done:
    ld      de, (#BIOS_TXTNAM)
    add     hl, de         ; HL = dest VRAM address
    ex      de, hl         ; DE = dest VRAM

    pop     bc             ; B = row, C = width
    ld      b, #0          ; BC = width (length)
    pop     hl             ; HL = src

    ld      iy,(#BIOS_EXPTBL-1)
    push    ix
    ld      ix,#BIOS_LDIRVM
    call    BIOS_CALSLT
    pop     ix
    ret
    __endasm;
}

int menu_ui_supports_80_column_mode(void) {
    return msx_version >= 1;
}

const char *menu_ui_status_text(const char *text_40, const char *text_80) {
    return use_80_columns ? text_80 : text_40;
}

static void menu_ui_copy_char_pattern(unsigned char source_char, unsigned char target_char)
{
    unsigned int base = ((unsigned int)vdp_reg4) << 11;
    unsigned int source_address = base + ((unsigned int)source_char * 8);
    unsigned int target_address = base + ((unsigned int)target_char * 8);

    for (unsigned char i = 0; i < 8; i++) {
        Vpoke(target_address + i, Vpeek(source_address + i));
    }
}

void menu_ui_set_text_mode(int enable_80) {
    if (enable_80) {
        text_columns = 80;
        use_80_columns = 1;
        name_col_width = NAME_COL_WIDTH_80;
    } else {
        text_columns = 40;
        use_80_columns = 0;
        name_col_width = NAME_COL_WIDTH;
    }
    __asm
    ld     iy,(#BIOS_EXPTBL-1)
    push   ix
    ld     ix,#BIOS_INITXT
    call   BIOS_CALSLT
    pop    ix
    __endasm;

    menu_ui_copy_char_pattern(MENU_UI_HLINE_SOURCE_CHAR, MENU_UI_HLINE_PRINT_CHAR);
}

void menu_ui_init_text_mode(void) {
    int enable_80 = (!MENU_FORCE_40_COLUMNS && menu_ui_supports_80_column_mode());
    menu_ui_set_text_mode(enable_80);
}

void invert_chars(unsigned char startChar, unsigned char endChar)
{
    unsigned int srcAddress, dstAddress;
    unsigned char patternByte;
    unsigned char i, c;
    unsigned int base = ((unsigned int)vdp_reg4) << 11;

    for (c = startChar; c <= endChar; c++)
    {
        srcAddress  = base + ((unsigned int)c * 8);
        dstAddress = srcAddress + (96 * 8);

        for (i = 0; i < 8; i++)
        {
            patternByte = Vpeek(srcAddress + i);
            patternByte = ~patternByte;
            Vpoke(dstAddress  + i, patternByte);
        }
    }
}

int menu_ui_try_toggle_columns(void) {
    int target_80 = !use_80_columns;
    if (target_80) {
        if (MENU_FORCE_40_COLUMNS) {
            menu_ui_wait_key_with_blinking_status("80-col off");
            menu_ui_clear_last_line();
            return 0;
        }
        if (!menu_ui_supports_80_column_mode()) {
            menu_ui_wait_key_with_blinking_status("No 80-column");
            menu_ui_clear_last_line();
            return 0;
        }
    }
    menu_ui_set_text_mode(target_80);
    invert_chars(32, 126);
    return 1;
}

unsigned char menu_ui_row_width(void) {
    return (unsigned char)(use_80_columns ? 80 : SCREEN_WIDTH);
}

void menu_ui_clear_rows(unsigned char start_row, unsigned char end_row) {
    if (start_row >= end_row) {
        return;
    }
    clear_rows_vram(start_row, end_row, menu_ui_row_width());
}

void menu_ui_print_title_line(void) {
    if (use_80_columns) {
        printf("MSX PICOVERSE 2350%44s[EXPLORER %s]", "", EXPLORER_VERSION);
    } else {
        printf("MSX PICOVERSE 2350%4s[EXPLORER %s]", "", EXPLORER_VERSION);
    }
}

void menu_ui_print_delimiter_line(void) {
    unsigned char width = use_80_columns ? 78 : 38;
    for (unsigned char i = 0; i < width; i++) {
        PrintChar(MENU_UI_HLINE_PRINT_CHAR);
    }
}

// File Hunter catalog label (" ROM"/" DSK"): list type column, detail screen
// name label and the list footer.
const char *menu_ui_fh_type_label(void) {
    return fh_catalog_type == CTRL_FH_TYPE_DSK ? " DSK" : " ROM";
}

void menu_ui_print_footer_line(void) {
    unsigned char width = menu_ui_row_width();
    unsigned char content_width = (unsigned char)(width - 2);
    unsigned char footer_len = menu_ui_shortcuts_length();
    unsigned char col = 11;
    const char *fmt = "Page: %02d/%02d%s";
    const char *label = "";

    if (menu_shortcut_selection == MENU_SHORTCUT_FILEHUNTER) {
        /* File Hunter: name the catalog being listed after the page counter. */
        if (use_80_columns) {
            fmt = "Page: %02d/%02d  Listing:%s";
            col = 25;
        } else {
            fmt = "Page:%02d/%02d%s";
            col = 14;
        }
        label = menu_ui_fh_type_label();
    }
    printf(fmt, currentPage, totalPages, label);

    while (col < content_width && (unsigned char)(content_width - col) > footer_len) {
        PrintChar(' ');
        col++;
    }

    col = (unsigned char)(col + menu_ui_render_shortcuts((unsigned char)(content_width - col)));

    while (col < content_width) {
        PrintChar(' ');
        col++;
    }
}

static unsigned char menu_ui_print_shortcut_token(const char *token, int selected) {
    unsigned char len = (unsigned char)strlen(token);

    for (unsigned char i = 0; i < len; i++) {
        unsigned char ch = (unsigned char)token[i];
        if (selected) {
            ch = (unsigned char)(ch + 96);
        }
        PrintChar(ch);
    }

    return len;
}

static const char *menu_ui_shortcut_token(unsigned char index) {
    if (use_80_columns) {
        switch (index) {
            case 0:  return "[F1 - Flash]";
            case 1:  return "[F2 - MicroSD]";
            default: return "[F3 - File Hunter]";
        }
    }
    switch (index) {
        case 0:  return "[F1-FL]";
        case 1:  return "[F2-SD]";
        default: return "[F3-FH]";
    }
}

static unsigned char menu_ui_shortcuts_length(void) {
    unsigned char total_len = 0;

    for (unsigned char i = 0; i < 3; i++) {
        total_len = (unsigned char)(total_len + (unsigned char)strlen(menu_ui_shortcut_token(i)));
    }

    return (unsigned char)(total_len + 2);
}

static unsigned char menu_ui_render_shortcuts(unsigned char content_width) {
    unsigned char total_len = 0;
    unsigned char col = 0;

    total_len = menu_ui_shortcuts_length();

    if (total_len > content_width) {
        total_len = content_width;
    }

    for (unsigned char i = 0; i < 3 && col < content_width; i++) {
        unsigned char token_len = menu_ui_print_shortcut_token(menu_ui_shortcut_token(i), menu_shortcut_selection == (unsigned char)(i + 1));
        col = (unsigned char)(col + token_len);
        if (i < 2 && col < content_width) {
            PrintChar(' ');
            col++;
        }
    }

    return total_len;
}

static void menu_ui_render_last_line(const char *left_text) {
    unsigned char width = menu_ui_row_width();
    unsigned char content_width = (unsigned char)(width - 2);
    const char *actions;
    char stop_char = 0;
    unsigned char right_len;
    unsigned char right_start = 0;
    unsigned char col = 0;

 
    actions = use_80_columns ?
            "[/ - Search] [  H - Help  ] [F4 - WiFi Config]" :
            "[/-Fnd] [H-Hlp] [F4-WF]";
    if (!left_text && menu_shortcut_selection == MENU_SHORTCUT_MICROSD) {
        left_text = (const char *)(CTRL_SD_PARTITION_INFO_BASE + 2);
        if (!use_80_columns) {
            const char *free_text = left_text;
            while (*free_text && *free_text != '(') {
                free_text++;
            }
            if (*free_text == '(' && (*((volatile unsigned char *)JIFFY) & 0x80)) {
                left_text = free_text + 1;
                stop_char = ')';
            } else {
                stop_char = '(';
            }
        }
    }
    

    right_len = (unsigned char)strlen(actions);

    Locate(0, 23);

    if (right_len < content_width) {
        right_start = (unsigned char)(content_width - right_len);
    }

    while (left_text && *left_text && *left_text != stop_char && col < right_start) {
        if (stop_char == '(' && *left_text == ' ' && left_text[1] == '(') {
            break;
        }
        PrintChar((unsigned char)*left_text++);
        col++;
    }

    while (col < right_start) {
        PrintChar(' ');
        col++;
    }

    while (*actions && col < content_width) {
        PrintChar((unsigned char)*actions++);
        col++;
    }

    while (col < content_width) {
        PrintChar(' ');
        col++;
    }
}

void menu_ui_render_menu_frame(void) {
    Locate(0, 0);
    menu_ui_print_title_line();
    Locate(0, 1);
    menu_ui_print_delimiter_line();
    Locate(0, 21);
    menu_ui_print_delimiter_line();
    Locate(0, 22);
    menu_ui_print_footer_line();
    menu_ui_render_last_line(0);
    frame_rendered = 1;
}

void menu_ui_render_detail_frame(void) {
    Locate(0, 0);
    menu_ui_print_title_line();
    Locate(0, 1);
    menu_ui_print_delimiter_line();
    menu_ui_clear_rows(2, 21);
    Locate(0, 21);
    menu_ui_print_delimiter_line();
    menu_ui_clear_rows(23, 24);
}

void menu_ui_update_footer_page(void) {
    Locate(0, 22);
    menu_ui_print_footer_line();
}

void menu_ui_clear_last_line(void) {
    menu_ui_render_last_line(0);
}

void menu_ui_print_last_line_text(const char *text) {
    menu_ui_render_last_line(text);
}

void menu_ui_blink_last_line(const char *text, unsigned char *visible, unsigned char *tick, unsigned char period) {
    if (++(*tick) >= period) {
        *tick = 0;
        *visible = !(*visible);
        if (*visible) {
            menu_ui_print_last_line_text(text);
        } else {
            menu_ui_render_last_line("");
        }
    }
}

void menu_ui_wait_key_with_blinking_status(const char *text) {
    unsigned char visible = 1;
    unsigned char tick = 0;

    menu_ui_print_last_line_text(text);
    while (!bios_chsns()) {
        delay_ms(20);
        menu_ui_blink_last_line(text, &visible, &tick, 8);
    }
    (void)bios_chget();
}

// menu_ui_read_line - Edit buffer (its current text is the starting value) after
// prompt on the last line. buffer must hold max_len + 1 bytes; the field is
// also limited to the room left on the line, which can shorten the starting
// text. Returns 1 on Enter after an edit, 2 on Enter with the text untouched,
// 0 on ESC and -1 on F4.
int menu_ui_read_line(const char *prompt, char *buffer, unsigned char max_len)
{
    unsigned char width = (unsigned char)(menu_ui_row_width() - 2);
    unsigned char col = (unsigned char)strlen(prompt);
    unsigned char len;
    unsigned char i;
    unsigned char edited = 0;
    char ch;

    if (max_len > (unsigned char)(width - col)) {
        max_len = (unsigned char)(width - col);
    }
    buffer[max_len] = '\0';
    len = (unsigned char)strlen(buffer);
    Locate(0, 23);
    printf("%s%s", prompt, buffer);
    for (i = (unsigned char)(col + len); i < width; i++) {
        PrintChar(' ');
    }

    while (1) {
        Locate((unsigned char)(col + len), 23);
        ch = (char)bios_chget();
        if (ch == 13) {
            return edited ? 1 : 2;
        }
        if (ch == 27) {
            return 0;
        }
        if (ch == MENU_KEY_F4_CONFIG) {
            return -1;
        }
        if (ch == 8 || ch == 127) {
            if (len > 0) {
                buffer[--len] = '\0';
                Locate((unsigned char)(col + len), 23);
                PrintChar(' ');
                edited = 1;
            }
        } else if (ch >= 32 && ch <= 126 && len < max_len) {
            PrintChar((unsigned char)ch);
            buffer[len++] = ch;
            buffer[len] = '\0';
            edited = 1;
        }
    }
}

void menu_ui_print_str_inverted_width(const char *str, unsigned char width)
{
    if (width == 0) {
        return;
    }
    unsigned char capped_width = width > 80 ? 80 : width;
    unsigned char i = 0;

    while (i < capped_width && str[i]) {
        PrintChar((unsigned char)(str[i] + 96));
        i++;
    }
    while (i < capped_width) {
        PrintChar((unsigned char)(' ' + 96));
        i++;
    }
}

void menu_ui_render_selectable_line(unsigned char row, const char *text, int selected) {
    unsigned char width = menu_ui_row_width();
    char buffer[81];
    unsigned char len = 0;
    unsigned char content_width;
    unsigned char selected_width;
    unsigned char i;

    if (width > 80) {
        width = 80;
    }
    content_width = width > 1 ? (unsigned char)(width - 1) : 0;
    selected_width = width > 3 ? (unsigned char)(width - 3) : content_width;

    if (text) {
        len = (unsigned char)strlen(text);
        if (len > content_width) {
            len = content_width;
        }
    }

    // Build the full row (selection marker + content) in RAM, applying the
    // inverted-glyph offset (+96) for the selected row, then write it to VRAM
    // in a single block transfer instead of one CHPUT per column.
    buffer[0] = selected ? '>' : ' ';
    if (selected) {
        for (i = 0; i < selected_width; i++) {
            unsigned char ch = (i < len) ? (unsigned char)text[i] : ' ';
            buffer[1 + i] = (char)(ch + 96);
        }
        for (i = selected_width; i < content_width; i++) {
            buffer[1 + i] = ' ';
        }
    } else {
        for (i = 0; i < content_width; i++) {
            buffer[1 + i] = (i < len) ? text[i] : ' ';
        }
    }

    blit_row_vram(row, buffer, width);
}
